zachrjt/digital-voltages-ps/main_board/main_board_top_view.png

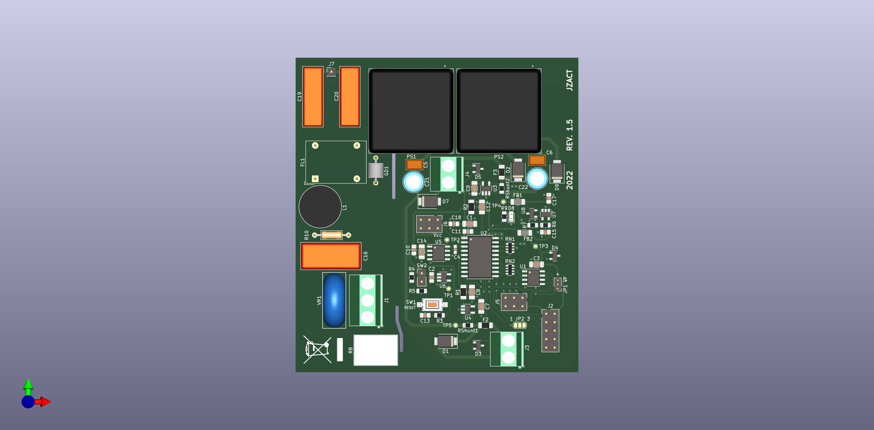
main_board/main_board_top_view.png
