zachrjt/digital-voltages-ps/Pictures/IMG_3281.JPG

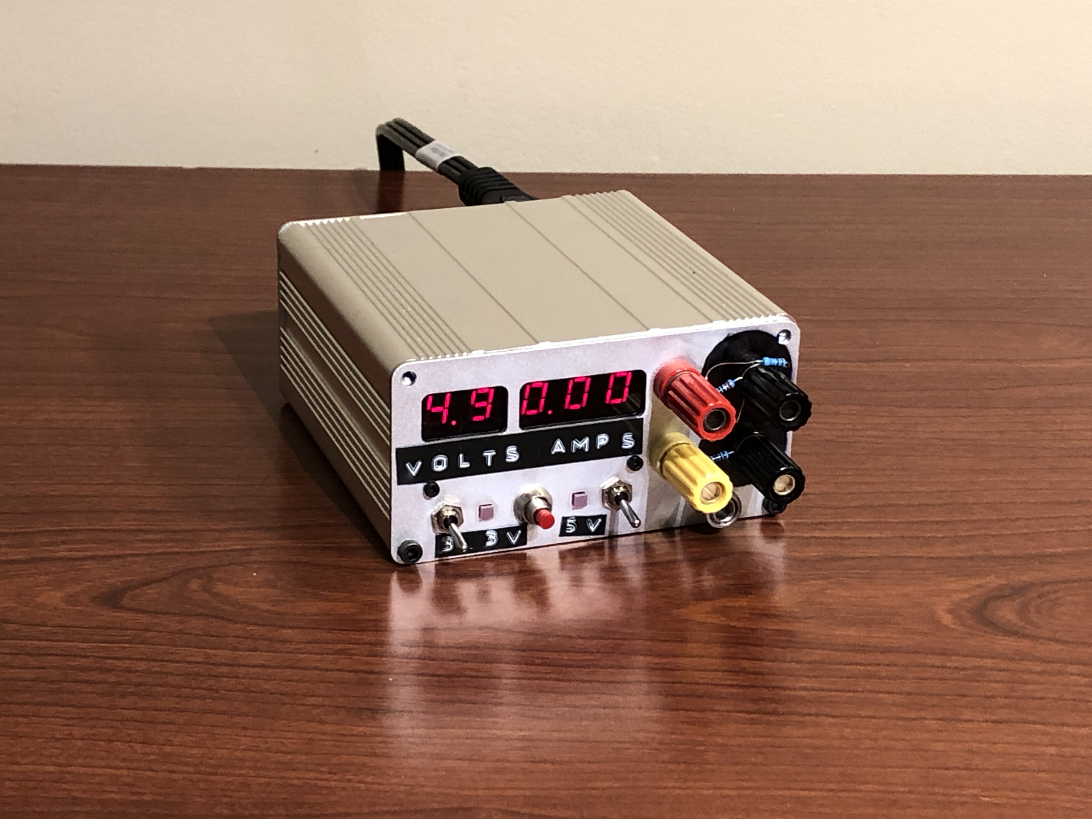
Pictures/IMG_3281.JPG
