zachrjt/digital-voltages-ps/Pictures/IMG_3283.JPG

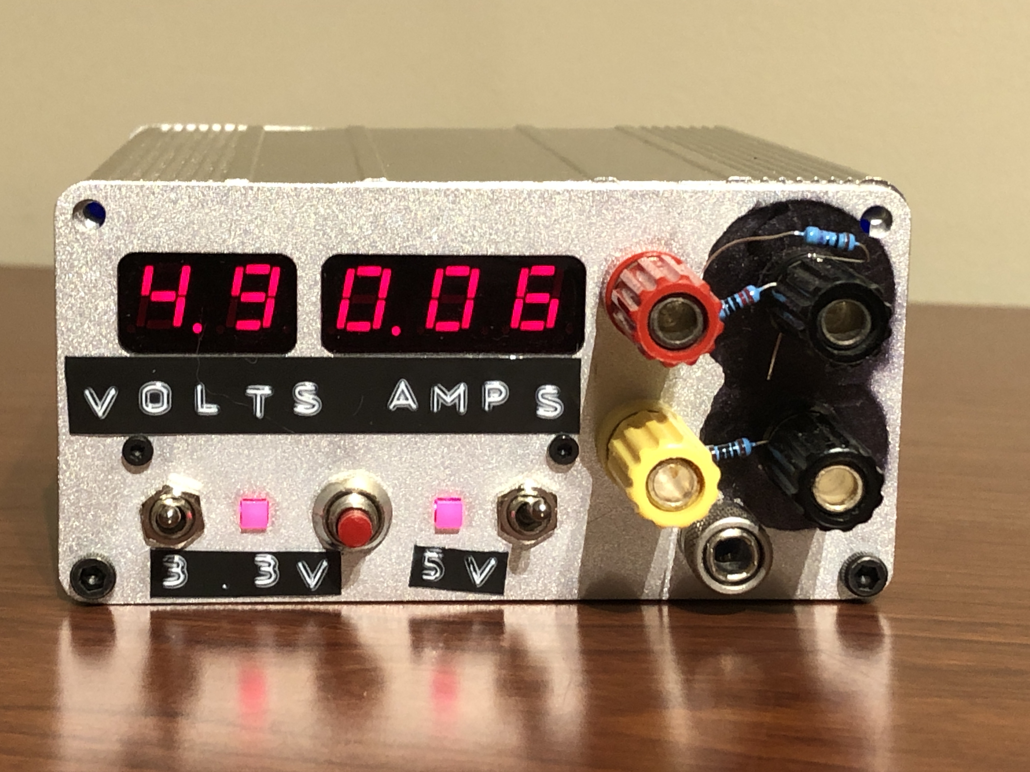
Pictures/IMG_3283.JPG
