zachrjt/digital-voltages-ps/Pictures/IMG_3284.JPG

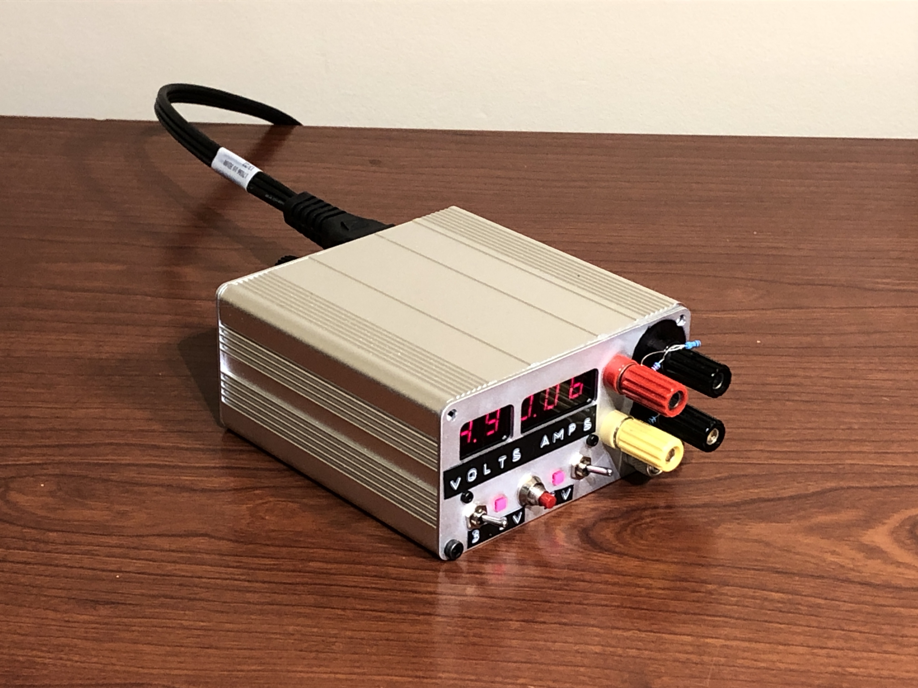
Pictures/IMG_3284.JPG
