zachrjt/digital-voltages-ps/Pictures/IMG_3286.JPG

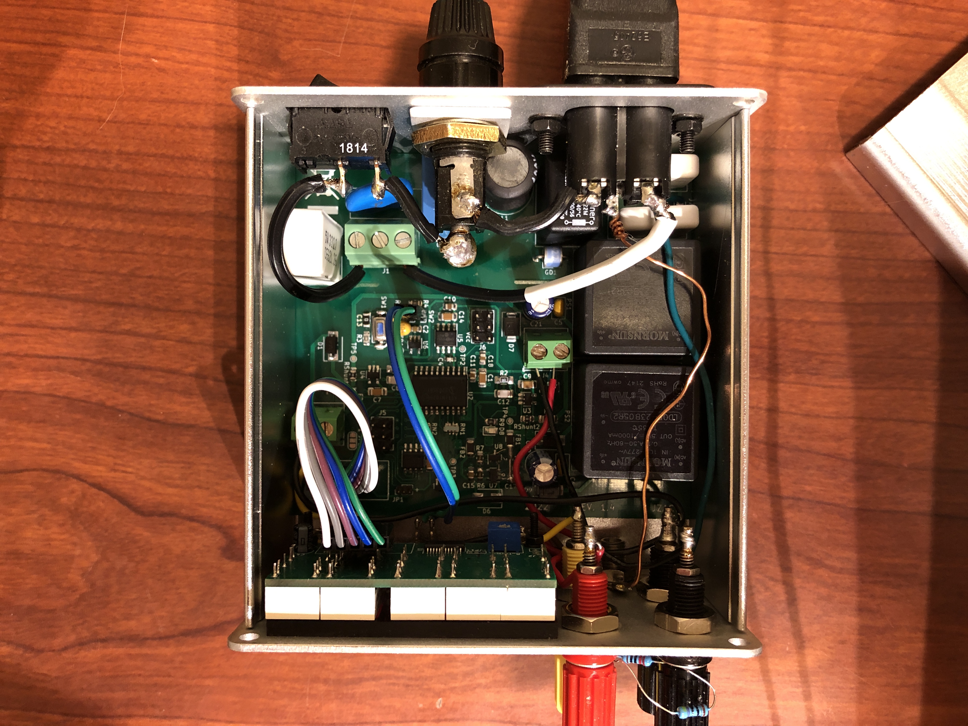
Pictures/IMG_3286.JPG
