zachrjt/digital-voltages-ps/Pictures/IMG_3287.JPG

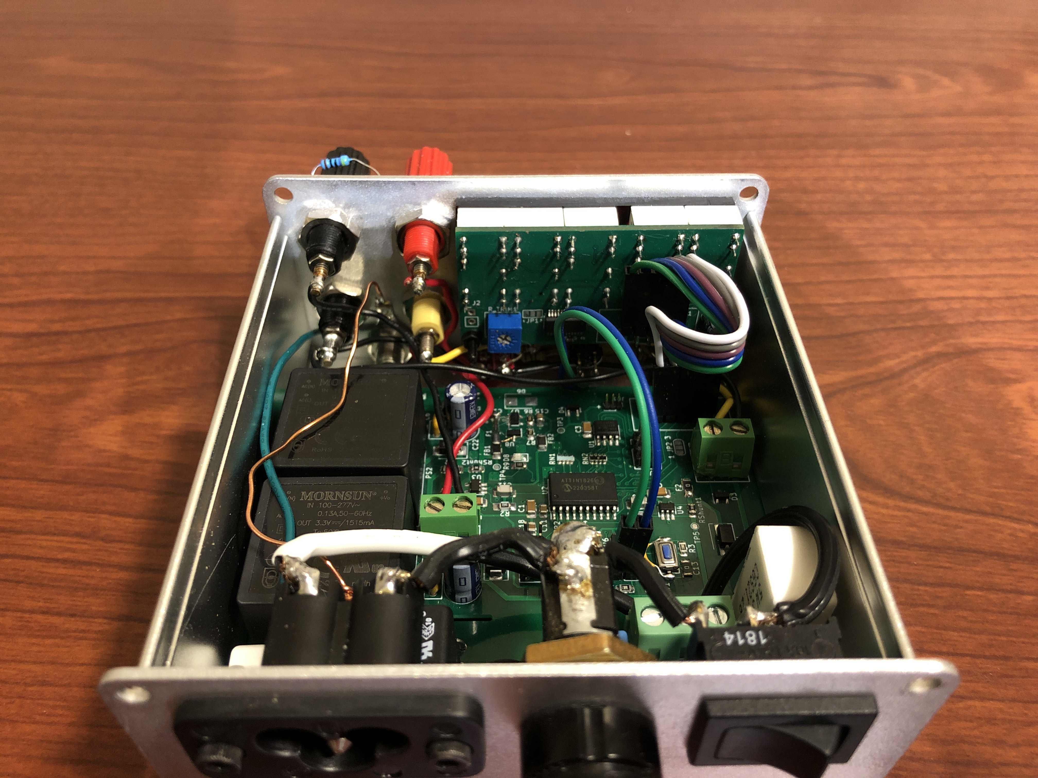
Pictures/IMG_3287.JPG
