zachrjt/digital-voltages-ps/Pictures/IMG_3288.JPG

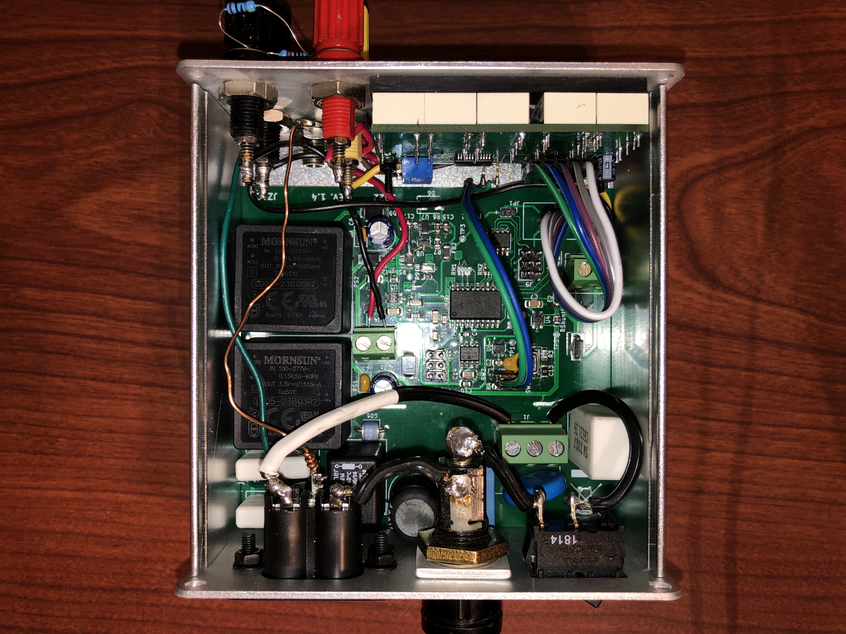
Pictures/IMG_3288.JPG
