zachrjt/digital-voltages-ps/code/main.h

#ifndef MAIN_H
#define MAIN_H

//Includes
#include <Wire.h>
#include "display.h"
#include "adc.h"

//Macros
#define CHIP_SELECT PIN_PC3
#define LED_PIN PIN_PA3
#define MODE_PIN PIN_PB3
#define i2c_addr 0x00

#endif
