zachrjt/digital-voltages-ps/code/adc.h

#ifndef ADC_H
#define ADC_H

//Includes

//Macros

//Function Declarations
void Voltage_ADCReading();
void Current_ADCReading();

//legacy code
//void Volt_ADCInitialize();
//void Current_ADCInitialize();



#endif
