zachrjt/digital-voltages-ps/Pictures/IMG_2989.JPG

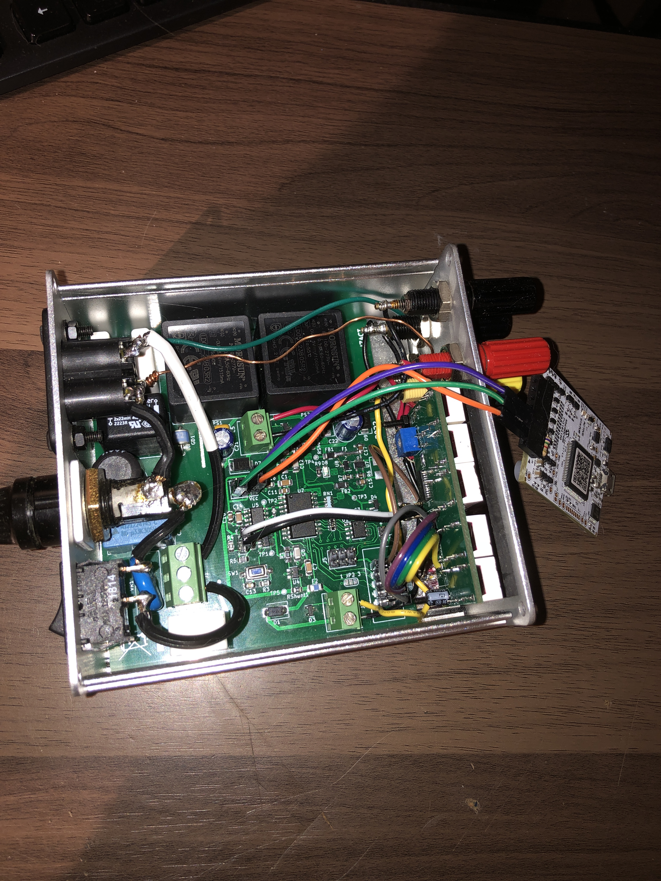
Pictures/IMG_2989.JPG
